tamago324/gku34/docs/rev0.3/assets/4_3.JPEG

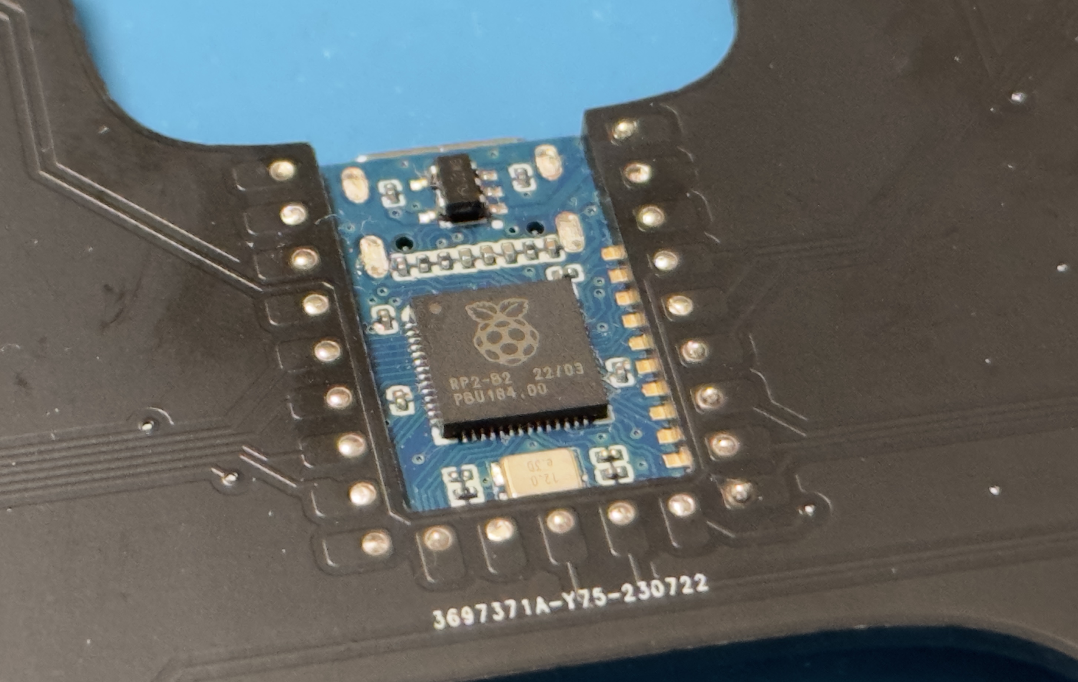
docs/rev0.3/assets/4_3.JPEG
