tamago324/gku34/docs/rev0.3/assets/51_1.png

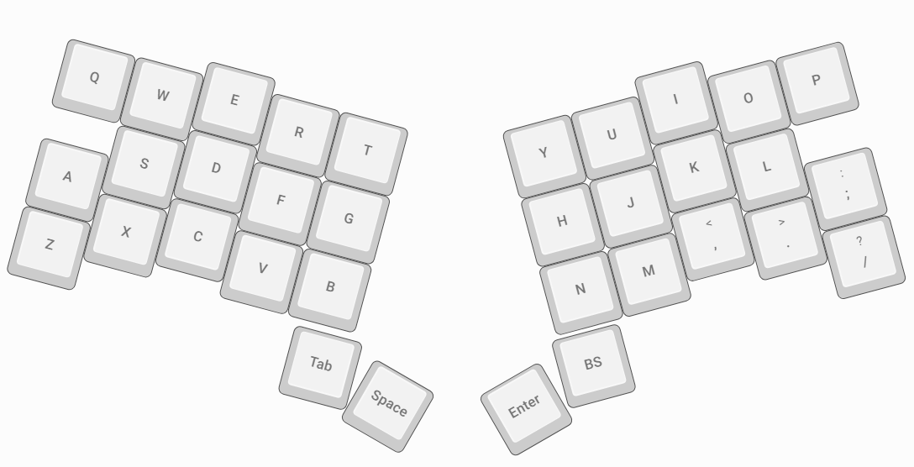
docs/rev0.3/assets/51_1.png
